zmacario/rugged-monitor/out/1-front.png

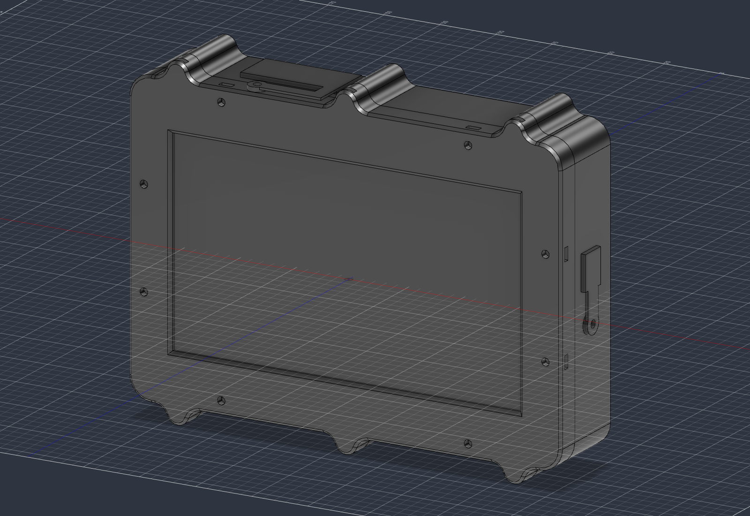
out/1-front.png
