zmacario/rugged-monitor/out/5-rear-cover-inside.png

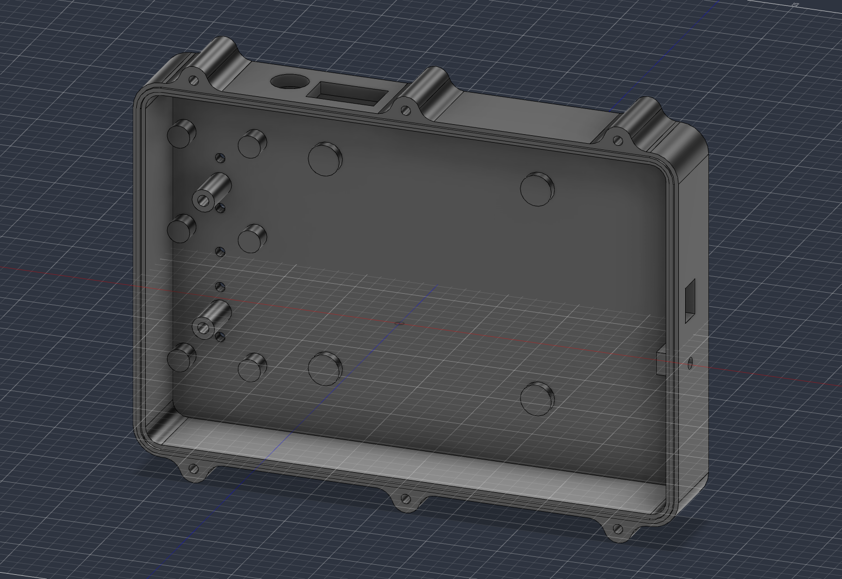
out/5-rear-cover-inside.png
