zmacario/rugged-monitor/out/6-front-bezel-inside.png

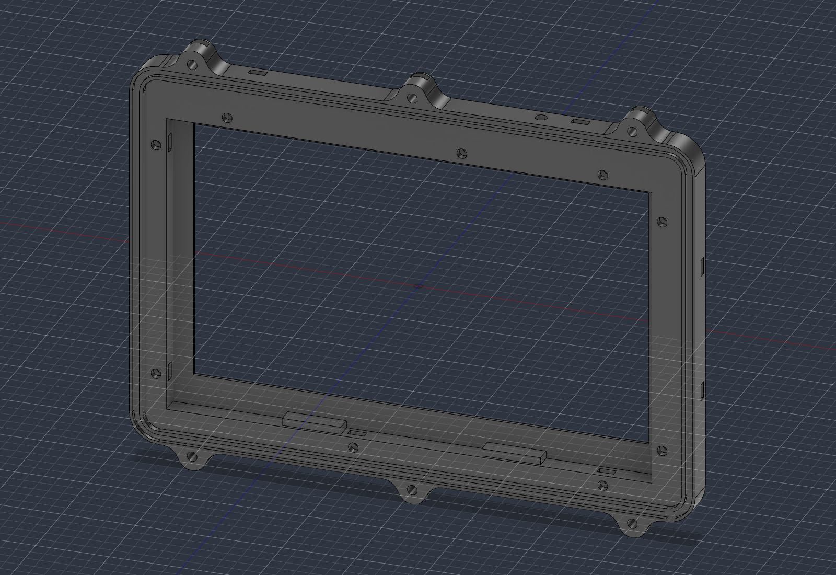
out/6-front-bezel-inside.png
