zmacario/rugged-monitor/out/7-keypad-frame.png

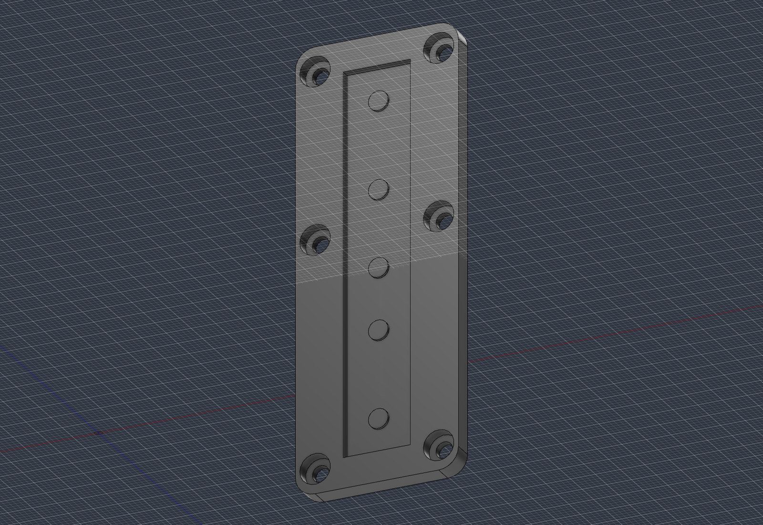
out/7-keypad-frame.png
