zmacario/rugged-monitor/out/8-keypad-strip-underside.png

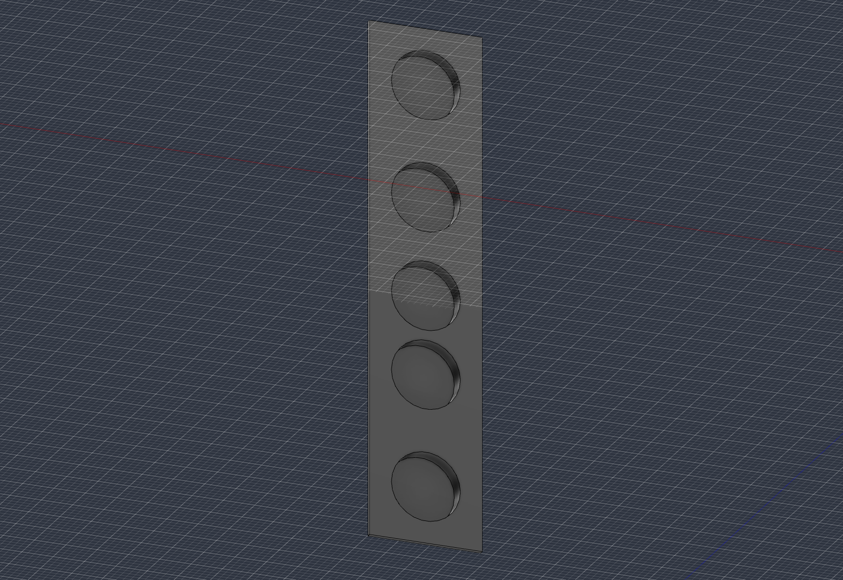
out/8-keypad-strip-underside.png
