zmacario/rugged-monitor/out/9-port-caps.png

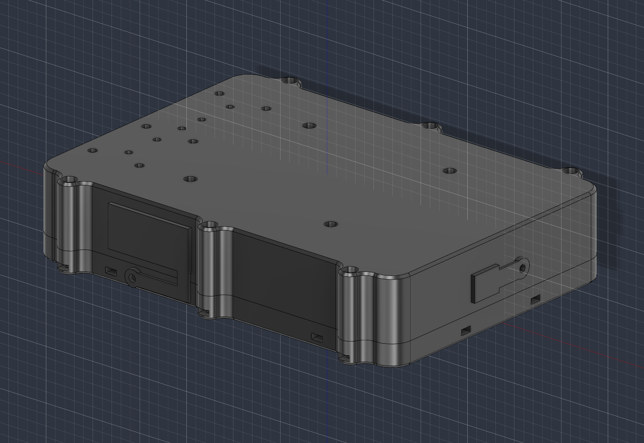
out/9-port-caps.png
