zmacario/rugged-monitor/out/15-stand-side-30.png

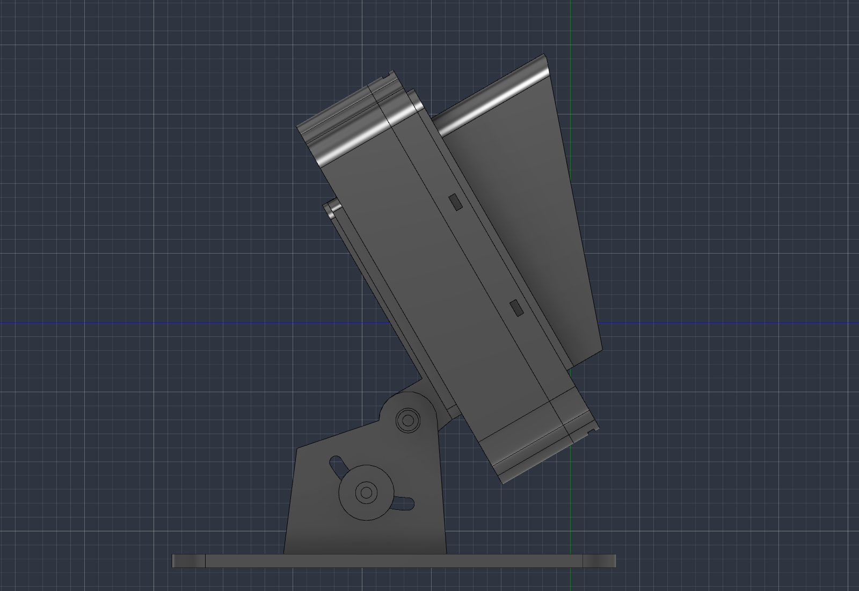
out/15-stand-side-30.png
