zmacario/rugged-monitor/out/keypad-frame.stl

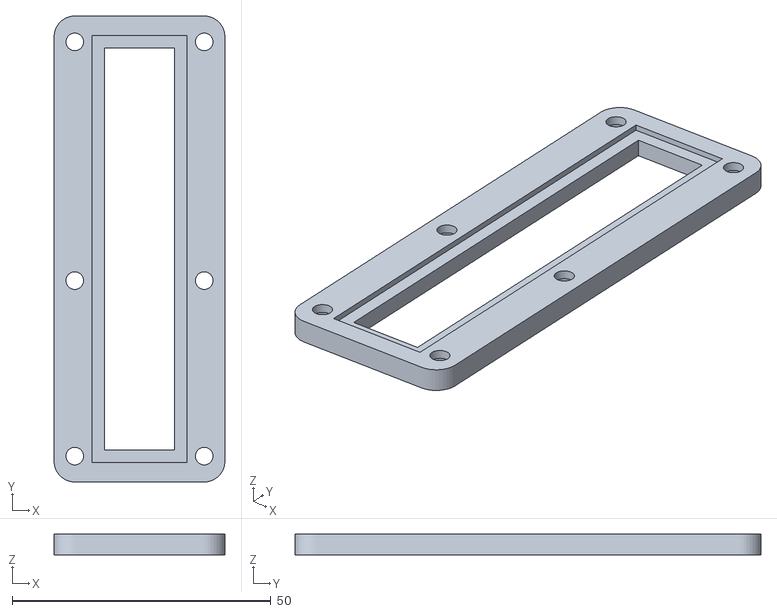
[picture p32: CAD file, 2026-10-09]
out/keypad-frame.stl
33.0 x 90.0 x 4.00
