zmacario/rugged-monitor/out/rear-cover.stl

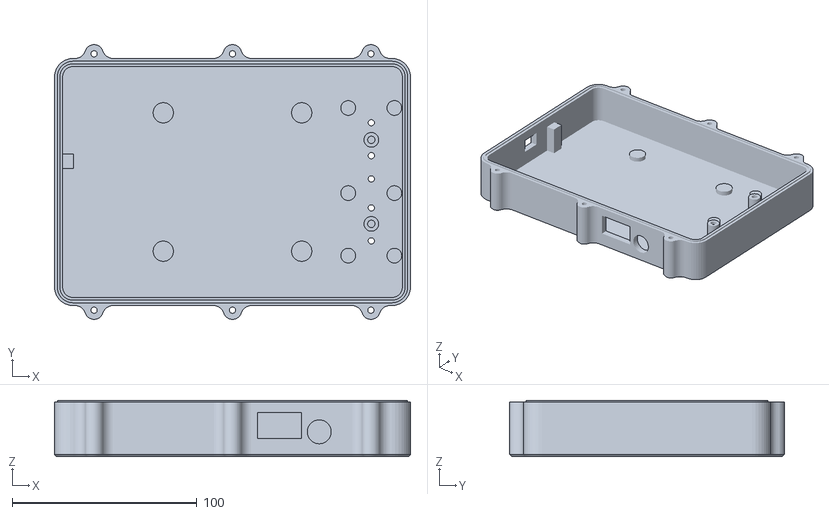
[picture p33: CAD file, 2026-10-09]
out/rear-cover.stl
192.9 x 148.8 x 30.6
